Wh1teRabbitHU/NixieClock/code/Core/Inc/display.h

#ifndef INC_DISPLAY_H_
#define INC_DISPLAY_H_

#include <stdint.h>
#include "main.h"
#include "binary.h"

void display_init();
void display_showNumber(uint16_t number);
void display_showTime(uint8_t hour, uint8_t minute);

#endif /* INC_DISPLAY_H_ */
